peterisza/temu-garden-lights-hack/controller-firmware/USBX/App/ux_device_descriptors.c

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

/* Includes ------------------------------------------------------------------*/
#include "ux_device_descriptors.h"

USBD_DevClassHandleTypeDef  USBD_Device_FS, USBD_Device_HS;

uint8_t UserClassInstance[USBD_MAX_CLASS_INTERFACES] = {
  CLASS_TYPE_HID,
};

uint8_t UserHIDInterface[] = {
  INTERFACE_HID_CUSTOM,
};

/* The generic device descriptor buffer that will be filled by builder
   Size of the buffer is the maximum possible device FS descriptor size. */
#if defined ( __ICCARM__ ) /* IAR Compiler */
#pragma data_alignment=4
#endif /* defined ( __ICCARM__ ) */
__ALIGN_BEGIN static uint8_t DevFrameWorkDesc_FS[USBD_FRAMEWORK_MAX_DESC_SZ] __ALIGN_END = {0};

/* The generic device descriptor buffer that will be filled by builder
   Size of the buffer is the maximum possible device HS descriptor size. */
#if defined ( __ICCARM__ ) /* IAR Compiler */
#pragma data_alignment=4
#endif /* defined ( __ICCARM__ ) */
__ALIGN_BEGIN static uint8_t DevFrameWorkDesc_HS[USBD_FRAMEWORK_MAX_DESC_SZ] __ALIGN_END = {0};

static uint8_t *pDevFrameWorkDesc_FS = DevFrameWorkDesc_FS;

static uint8_t *pDevFrameWorkDesc_HS = DevFrameWorkDesc_HS;
/* String Device Framework :
 Byte 0 and 1 : Word containing the language ID : 0x0904 for US
 Byte 2       : Byte containing the index of the descriptor
 Byte 3       : Byte containing the length of the descriptor string
*/
#if defined ( __ICCARM__ ) /* IAR Compiler */
#pragma data_alignment=4
#endif /* defined ( __ICCARM__ ) */
__ALIGN_BEGIN UCHAR USBD_string_framework[USBD_STRING_FRAMEWORK_MAX_LENGTH]
__ALIGN_END = {0};

/* Multiple languages are supported on the device, to add
   a language besides English, the Unicode language code must
   be appended to the language_id_framework array and the length
   adjusted accordingly. */

#if defined ( __ICCARM__ ) /* IAR Compiler */
#pragma data_alignment=4
#endif /* defined ( __ICCARM__ ) */
__ALIGN_BEGIN UCHAR USBD_language_id_framework[LANGUAGE_ID_MAX_LENGTH]
__ALIGN_END = {0};

#if USBD_HID_CUSTOM_ACTIVATED == 1U

#if defined ( __ICCARM__ ) /* IAR Compiler */
#pragma data_alignment=4
#endif /* defined ( __ICCARM__ ) */
__ALIGN_BEGIN uint8_t USBD_CustomHID_ReportDesc[]
__ALIGN_END =
{
  /* USER CODE BEGIN USBD_CustomHID_ReportDesc */
	  0x06, 0x00, 0xFF,  // Usage Page (Vendor Defined 0xFF00)
	  0x09, 0x01,        // Usage (Vendor Usage 1)
	  0xA1, 0x01,        // Collection (Application)

	  // INPUT REPORT (MCU -> PC): 64 bájt
	  0x09, 0x01,        // Usage
	  0x15, 0x00,        // Logical Minimum (0)
	  0x26, 0xFF, 0x00,  // Logical Maximum (255)
	  0x75, 0x08,        // Report Size (8 bits)
	  0x95, 0x40,        // Report Count (64 bytes = 0x40)
	  0x81, 0x02,        // Input (Data, Variable, Absolute)

	  // OUTPUT REPORT (PC -> MCU): 64 bájt
	  0x09, 0x01,        // Usage
	  0x15, 0x00,        // Logical Minimum (0)
	  0x26, 0xFF, 0x00,  // Logical Maximum (255)
	  0x75, 0x08,        // Report Size (8 bits)
	  0x95, 0x40,        // Report Count (64 bytes = 0x40)
	  0x91, 0x02,        // Output (Data, Variable, Absolute)

  /* USER CODE END USBD_CustomHID_ReportDesc */
  0xc0                          /* End Collection                       */
};

#endif /* USBD_HID_CUSTOM_ACTIVATED == 1U */

static void USBD_Desc_GetString(uint8_t *desc, uint8_t *Buffer, uint16_t *len);
static uint8_t USBD_Desc_GetLen(uint8_t *buf);

static uint8_t *USBD_Device_Framework_Builder(USBD_DevClassHandleTypeDef *pdev,
                                              uint8_t *pDevFrameWorkDesc,
                                              uint8_t *UserClassInstance,
                                              uint8_t Speed);

static uint8_t USBD_FrameWork_AddToConfDesc(USBD_DevClassHandleTypeDef *pdev,
                                            uint8_t Speed,
                                            uint8_t *pCmpstConfDesc);

static uint8_t USBD_FrameWork_AddClass(USBD_DevClassHandleTypeDef *pdev,
                                       USBD_CompositeClassTypeDef class,
                                       uint8_t cfgidx, uint8_t Speed,
                                       uint8_t *pCmpstConfDesc);

static uint8_t USBD_FrameWork_FindFreeIFNbr(USBD_DevClassHandleTypeDef *pdev);

static void USBD_FrameWork_AddConfDesc(uint32_t Conf, uint32_t *pSze);

static void USBD_FrameWork_AssignEp(USBD_DevClassHandleTypeDef *pdev, uint8_t Add,
                                    uint8_t Type, uint32_t Sze);

#if USBD_HID_CLASS_ACTIVATED == 1U
static void USBD_FrameWork_HID_Desc(USBD_DevClassHandleTypeDef *pdev,
                                    uint32_t pConf, uint32_t *Sze);
#endif /* USBD_HID_CLASS_ACTIVATED == 1U */

/**
  * @brief  USBD_Get_Device_Framework_Speed
  *         Return the device speed descriptor
  * @param  Speed : HIGH or FULL SPEED flag
  * @param  length : length of HIGH or FULL SPEED array
  * @retval Pointer to descriptor buffer
  */
uint8_t *USBD_Get_Device_Framework_Speed(uint8_t Speed, ULONG *Length)
{
  uint8_t *pFrameWork = NULL;
  if (USBD_FULL_SPEED == Speed)
  {
    USBD_Device_Framework_Builder(&USBD_Device_FS, pDevFrameWorkDesc_FS,
                                  UserClassInstance, Speed);

    /* Get the length of USBD_device_framework_full_speed */
    *Length = (ULONG)(USBD_Device_FS.CurrDevDescSz + USBD_Device_FS.CurrConfDescSz);

    pFrameWork = pDevFrameWorkDesc_FS;
  }
  else
  {
    USBD_Device_Framework_Builder(&USBD_Device_HS, pDevFrameWorkDesc_HS,
                                  UserClassInstance, Speed);

    /* Get the length of USBD_device_framework_high_speed */
    *Length = (ULONG)(USBD_Device_HS.CurrDevDescSz + USBD_Device_HS.CurrConfDescSz);

    pFrameWork = pDevFrameWorkDesc_HS;
  }
  return pFrameWork;
}

/**
  * @brief  USBD_Get_String_Framework
  *         Return the language_id_framework
  * @param  Length : Length of String_Framework
  * @retval Pointer to language_id_framework buffer
  */
uint8_t *USBD_Get_String_Framework(ULONG *Length)
{
  uint16_t len = 0U;
  uint8_t count = 0U;

  /* Set the Manufacturer language Id and index in USBD_string_framework */
  USBD_string_framework[count++] = USBD_LANGID_STRING & 0xFF;
  USBD_string_framework[count++] = USBD_LANGID_STRING >> 8;
  USBD_string_framework[count++] = USBD_IDX_MFC_STR;

  /* Set the Manufacturer string in string_framework */
  USBD_Desc_GetString((uint8_t *)USBD_MANUFACTURER_STRING, USBD_string_framework + count, &len);

  /* Set the Product language Id and index in USBD_string_framework */
  count += len + 1;
  USBD_string_framework[count++] = USBD_LANGID_STRING & 0xFF;
  USBD_string_framework[count++] = USBD_LANGID_STRING >> 8;
  USBD_string_framework[count++] = USBD_IDX_PRODUCT_STR;

  /* Set the Product string in USBD_string_framework */
  USBD_Desc_GetString((uint8_t *)USBD_PRODUCT_STRING, USBD_string_framework + count, &len);

  /* Set Serial language Id and index in string_framework */
  count += len + 1;
  USBD_string_framework[count++] = USBD_LANGID_STRING & 0xFF;
  USBD_string_framework[count++] = USBD_LANGID_STRING >> 8;
  USBD_string_framework[count++] = USBD_IDX_SERIAL_STR;

  /* Set the Serial number in USBD_string_framework */
  USBD_Desc_GetString((uint8_t *)USBD_SERIAL_NUMBER, USBD_string_framework + count, &len);

  /* Get the length of USBD_string_framework */
  *Length = strlen((const char *)USBD_string_framework);

  return USBD_string_framework;
}

/**
  * @brief  USBD_Get_Language_Id_Framework
  *         Return the language_id_framework
  * @param  Length : Length of Language_Id_Framework
  * @retval Pointer to language_id_framework buffer
  */
uint8_t *USBD_Get_Language_Id_Framework(ULONG *Length)
{
  uint8_t count = 0U;

  /* Set the language Id in USBD_language_id_framework */
  USBD_language_id_framework[count++] = USBD_LANGID_STRING & 0xFF;
  USBD_language_id_framework[count++] = USBD_LANGID_STRING >> 8;

  /* Get the length of USBD_language_id_framework */
  *Length = strlen((const char *)USBD_language_id_framework);

  return USBD_language_id_framework;
}

/**
  * @brief  USBD_Get_Interface_Number
  *         Return interface number
  * @param  class_type : Device class type
  * @param  interface_type : Device interface type
  * @retval interface number
  */
uint16_t USBD_Get_Interface_Number(uint8_t class_type, uint8_t interface_type)
{
  uint8_t itf_num = 0U;
  uint8_t idx = 0U;

  for(idx = 0; idx < USBD_MAX_SUPPORTED_CLASS; idx++)
  {
    if ((USBD_Device_FS.tclasslist[idx].ClassType == class_type) &&
        (USBD_Device_FS.tclasslist[idx].InterfaceType == interface_type))
    {
      itf_num = USBD_Device_FS.tclasslist[idx].Ifs[0];
    }
  }

  return itf_num;
}

/**
  * @brief  USBD_Get_Configuration_Number
  *         Return configuration number
  * @param  class_type : Device class type
  * @param  interface_type : Device interface type
  * @retval configuration number
  */
uint16_t USBD_Get_Configuration_Number(uint8_t class_type, uint8_t interface_type)
{
  uint8_t cfg_num = 1U;

  return cfg_num;
}

#if USBD_HID_CLASS_ACTIVATED == 1U
/**
  * @brief  USBD_HID_ReportDesc
  *         Return the device HID Report Descriptor
  * @param  hid_type : HID Device type
  * @retval Pointer to HID Report Descriptor buffer
  */
uint8_t *USBD_HID_ReportDesc(uint8_t hid_type)
{
  uint8_t *pHidReportDesc = NULL;

  switch(hid_type)
  {
    case INTERFACE_HID_CUSTOM:
      pHidReportDesc = USBD_CustomHID_ReportDesc;
      break;
    default:
      break;
  }

  return pHidReportDesc;
}

/**
  * @brief  USBD_HID_ReportDesc_length
  *         Return the device HID Report Descriptor
  * @param  hid_type : HID Device type
  * @retval Size of HID Report Descriptor buffer
  */
uint16_t USBD_HID_ReportDesc_length(uint8_t hid_type)
{
  uint16_t ReportDesc_Size = 0;

  switch(hid_type)
  {
    case INTERFACE_HID_CUSTOM:
      ReportDesc_Size = sizeof(USBD_CustomHID_ReportDesc);
      break;
    default:
      break;
  }

  return ReportDesc_Size;
}
#endif /* USBD_HID_CLASS_ACTIVATED == 1U */

/**
  * @brief  USBD_Desc_GetString
  *         Convert ASCII string into Unicode one
  * @param  desc : descriptor buffer
  * @param  Unicode : Formatted string buffer (Unicode)
  * @param  len : descriptor length
  * @retval None
  */
static void USBD_Desc_GetString(uint8_t *desc, uint8_t *unicode, uint16_t *len)
{
  uint8_t idx = 0U;
  uint8_t *pdesc;

  if (desc == NULL)
  {
    return;
  }

  pdesc = desc;
  *len = (uint16_t)USBD_Desc_GetLen(pdesc);

  unicode[idx++] = *(uint8_t *)len;

  while (*pdesc != (uint8_t)'\0')
  {
    unicode[idx++] = *pdesc;
    pdesc++;
  }
}

/**
  * @brief  USBD_Desc_GetLen
  *         return the string length
  * @param  buf : pointer to the ASCII string buffer
  * @retval string length
  */
static uint8_t USBD_Desc_GetLen(uint8_t *buf)
{
  uint8_t  len = 0U;
  uint8_t *pbuff = buf;

  while (*pbuff != (uint8_t)'\0')
  {
    len++;
    pbuff++;
  }

  return len;
}

/**
  * @brief  USBD_Device_Framework_Builder
  *         Device Framework builder
  * @param  pdev: device instance
  * @param  pDevFrameWorkDesc: Pointer to the device framework descriptor
  * @param  UserClassInstance: type of the class to be added
  * @param  Speed: Speed parameter HS or FS
  * @retval status
  */
static uint8_t *USBD_Device_Framework_Builder(USBD_DevClassHandleTypeDef *pdev,
                                              uint8_t *pDevFrameWorkDesc,
                                              uint8_t *UserClassInstance,
                                              uint8_t Speed)
{
  static USBD_DeviceDescTypedef   *pDevDesc;
  static USBD_DevQualiDescTypedef *pDevQualDesc;
  uint8_t Idx_Instance = 0U;

  /* Set Dev and conf descriptors size to 0 */
  pdev->CurrConfDescSz = 0U;
  pdev->CurrDevDescSz = 0U;

  /* Set the pointer to the device descriptor area*/
  pDevDesc = (USBD_DeviceDescTypedef *)pDevFrameWorkDesc;

  /* Start building the generic device descriptor common part */
  pDevDesc->bLength = (uint8_t)sizeof(USBD_DeviceDescTypedef);
  pDevDesc->bDescriptorType = UX_DEVICE_DESCRIPTOR_ITEM;
  pDevDesc->bcdUSB = USB_BCDUSB;
  pDevDesc->bDeviceClass = 0x00;
  pDevDesc->bDeviceSubClass = 0x00;
  pDevDesc->bDeviceProtocol = 0x00;
  pDevDesc->bMaxPacketSize = USBD_MAX_EP0_SIZE;
  pDevDesc->idVendor = USBD_VID;
  pDevDesc->idProduct = USBD_PID;
  pDevDesc->bcdDevice = 0x0200;
  pDevDesc->iManufacturer = USBD_IDX_MFC_STR;
  pDevDesc->iProduct = USBD_IDX_PRODUCT_STR;
  pDevDesc->iSerialNumber = USBD_IDX_SERIAL_STR;
  pDevDesc->bNumConfigurations = USBD_MAX_NUM_CONFIGURATION;
  pdev->CurrDevDescSz += (uint32_t)sizeof(USBD_DeviceDescTypedef);

  /* Check if USBx is in high speed mode to add qualifier descriptor */
  if (Speed == USBD_HIGH_SPEED)
  {
    pDevQualDesc = (USBD_DevQualiDescTypedef *)(pDevFrameWorkDesc + pdev->CurrDevDescSz);
    pDevQualDesc->bLength = (uint8_t)sizeof(USBD_DevQualiDescTypedef);
    pDevQualDesc->bDescriptorType = UX_DEVICE_QUALIFIER_DESCRIPTOR_ITEM;
    pDevQualDesc->bcdDevice = 0x0200;
    pDevQualDesc->Class = 0x00;
    pDevQualDesc->SubClass = 0x00;
    pDevQualDesc->Protocol = 0x00;
    pDevQualDesc->bMaxPacketSize = 0x40;
    pDevQualDesc->bNumConfigurations = 0x01;
    pDevQualDesc->bReserved = 0x00;
    pdev->CurrDevDescSz += (uint32_t)sizeof(USBD_DevQualiDescTypedef);
  }

  /* Build the device framework */
  while (Idx_Instance < USBD_MAX_SUPPORTED_CLASS)
  {
    if ((pdev->classId < USBD_MAX_SUPPORTED_CLASS) &&
        (pdev->NumClasses < USBD_MAX_SUPPORTED_CLASS) &&
        (UserClassInstance[Idx_Instance] != CLASS_TYPE_NONE))
    {
      /* Call the composite class builder */
      (void)USBD_FrameWork_AddClass(pdev,
                                    (USBD_CompositeClassTypeDef)UserClassInstance[Idx_Instance],
                                    0, Speed,
                                    (pDevFrameWorkDesc + pdev->CurrDevDescSz));

      /* Increment the ClassId for the next occurrence */
      pdev->classId ++;
      pdev->NumClasses ++;
    }

    Idx_Instance++;
  }

  /* Check if there is a composite class and update device class */
  if (pdev->NumClasses > 1)
  {
    pDevDesc->bDeviceClass = 0xEF;
    pDevDesc->bDeviceSubClass = 0x02;
    pDevDesc->bDeviceProtocol = 0x01;
  }
  else
  {
    /* Check if the CDC ACM class is set and update device class */
    if (UserClassInstance[0] == CLASS_TYPE_CDC_ACM)
    {
      pDevDesc->bDeviceClass = 0x02;
      pDevDesc->bDeviceSubClass = 0x02;
      pDevDesc->bDeviceProtocol = 0x00;
    }
  }

  return pDevFrameWorkDesc;
}

/**
  * @brief  USBD_FrameWork_AddClass
  *         Register a class in the class builder
  * @param  pdev: device instance
  * @param  class: type of the class to be added (from USBD_CompositeClassTypeDef)
  * @param  cfgidx: configuration index
  * @param  speed: device speed
  * @param  pCmpstConfDesc: to composite device configuration descriptor
  * @retval status
  */
uint8_t  USBD_FrameWork_AddClass(USBD_DevClassHandleTypeDef *pdev,
                                 USBD_CompositeClassTypeDef class,
                                 uint8_t cfgidx, uint8_t Speed,
                                 uint8_t *pCmpstConfDesc)
{

  static uint8_t interface_idx = 0U;

  if ((pdev->classId < USBD_MAX_SUPPORTED_CLASS) &&
      (pdev->tclasslist[pdev->classId].Active == 0U))
  {
    /* Store the class parameters in the global tab */
    pdev->tclasslist[pdev->classId].ClassId = pdev->classId;
    pdev->tclasslist[pdev->classId].Active = 1U;
    pdev->tclasslist[pdev->classId].ClassType = class;

    if (class == CLASS_TYPE_HID)
    {
      pdev->tclasslist[pdev->classId].InterfaceType = UserHIDInterface[interface_idx];

      interface_idx++;

      if (interface_idx == sizeof(UserHIDInterface))
      {
        interface_idx = 0U;
      }
    }

    /* Call configuration descriptor builder and endpoint configuration builder */
    if (USBD_FrameWork_AddToConfDesc(pdev, Speed, pCmpstConfDesc) != UX_SUCCESS)
    {
      return UX_ERROR;
    }
  }

  UNUSED(cfgidx);

  return UX_SUCCESS;
}

/**
  * @brief  USBD_FrameWork_AddToConfDesc
  *         Add a new class to the configuration descriptor
  * @param  pdev: device instance
  * @param  Speed: device speed
  * @param  pCmpstConfDesc: to composite device configuration descriptor
  * @retval status
  */
uint8_t  USBD_FrameWork_AddToConfDesc(USBD_DevClassHandleTypeDef *pdev, uint8_t Speed,
                                      uint8_t *pCmpstConfDesc)
{
  uint8_t interface = 0U;

  /* The USB drivers do not set the speed value, so set it here before starting */
  pdev->Speed = Speed;

  /* start building the config descriptor common part */
  if (pdev->classId == 0U)
  {
    /* Add configuration and IAD descriptors */
    USBD_FrameWork_AddConfDesc((uint32_t)pCmpstConfDesc, &pdev->CurrConfDescSz);
  }

  switch (pdev->tclasslist[pdev->classId].ClassType)
  {

#if USBD_HID_CLASS_ACTIVATED == 1U

    case CLASS_TYPE_HID:

      switch(pdev->tclasslist[pdev->classId].InterfaceType)
      {

#if USBD_HID_CUSTOM_ACTIVATED == 1U

        case INTERFACE_HID_CUSTOM:

          /* Find the first available interface slot and Assign number of interfaces */
          interface = USBD_FrameWork_FindFreeIFNbr(pdev);
          pdev->tclasslist[pdev->classId].NumIf = 1U;
          pdev->tclasslist[pdev->classId].Ifs[0] = interface;

          /* Assign endpoint numbers */
          pdev->tclasslist[pdev->classId].NumEps = 2U; /* EP_IN, EP_OUT */

          /* Check the current speed to assign endpoints */
          if (pdev->Speed == USBD_HIGH_SPEED)
          {
            /* Assign IN Endpoint */
            USBD_FrameWork_AssignEp(pdev, USBD_HID_CUSTOM_EPIN_ADDR,
                                    USBD_EP_TYPE_INTR, USBD_HID_CUSTOM_EPIN_HS_MPS);

            /* Assign OUT Endpoint */
            USBD_FrameWork_AssignEp(pdev, USBD_HID_CUSTOM_EPOUT_ADDR,
                                    USBD_EP_TYPE_INTR, USBD_HID_CUSTOM_EPOUT_HS_MPS);
          }
          else
          {
            /* Assign IN Endpoint */
            USBD_FrameWork_AssignEp(pdev, USBD_HID_CUSTOM_EPIN_ADDR,
                                    USBD_EP_TYPE_INTR, USBD_HID_CUSTOM_EPIN_FS_MPS);

            /* Assign OUT Endpoint */
            USBD_FrameWork_AssignEp(pdev, USBD_HID_CUSTOM_EPOUT_ADDR,
                                    USBD_EP_TYPE_INTR, USBD_HID_CUSTOM_EPOUT_FS_MPS);
          }

          /* Configure and Append the Descriptor */
          USBD_FrameWork_HID_Desc(pdev, (uint32_t)pCmpstConfDesc, &pdev->CurrConfDescSz);

          break;

#endif /* USBD_HID_CUSTOM_ACTIVATED == 1U */

        default:
          break;
      }

      break;
#endif /* USBD_HID_CLASS_ACTIVATED == 1U */

    default:
      break;
  }

  return UX_SUCCESS;
}

/**
  * @brief  USBD_FrameWork_FindFreeIFNbr
  *         Find the first interface available slot
  * @param  pdev: device instance
  * @retval The interface number to be used
  */
static uint8_t USBD_FrameWork_FindFreeIFNbr(USBD_DevClassHandleTypeDef *pdev)
{
  uint32_t idx = 0U;

  /* Unroll all already activated classes */
  for (uint32_t i = 0U; i < pdev->NumClasses; i++)
  {
    /* Unroll each class interfaces */
    for (uint32_t j = 0U; j < pdev->tclasslist[i].NumIf; j++)
    {
      /* Increment the interface counter index */
      idx++;
    }
  }

  /* Return the first available interface slot */
  return (uint8_t)idx;
}

/**
  * @brief  USBD_FrameWork_AddConfDesc
  *         Add a new class to the configuration descriptor
  * @param  Conf: configuration descriptor
  * @param  pSze: pointer to the configuration descriptor size
  * @retval none
  */
static void  USBD_FrameWork_AddConfDesc(uint32_t Conf, uint32_t *pSze)
{
  /* Intermediate variable to comply with MISRA-C Rule 11.3 */
  USBD_ConfigDescTypedef *ptr = (USBD_ConfigDescTypedef *)Conf;

  ptr->bLength = (uint8_t)sizeof(USBD_ConfigDescTypedef);
  ptr->bDescriptorType = USB_DESC_TYPE_CONFIGURATION;
  ptr->wDescriptorLength = 0U;
  ptr->bNumInterfaces = 0U;
  ptr->bConfigurationValue = 1U;
  ptr->iConfiguration = USBD_CONFIG_STR_DESC_IDX;
  ptr->bmAttributes = USBD_CONFIG_BMATTRIBUTES;
  ptr->bMaxPower = USBD_CONFIG_MAXPOWER;
  *pSze += sizeof(USBD_ConfigDescTypedef);
}

/**
  * @brief  USBD_FrameWork_AssignEp
  *         Assign and endpoint
  * @param  pdev: device instance
  * @param  Add: Endpoint address
  * @param  Type: Endpoint type
  * @param  Sze: Endpoint max packet size
  * @retval none
  */
static void  USBD_FrameWork_AssignEp(USBD_DevClassHandleTypeDef *pdev,
                                     uint8_t Add, uint8_t Type, uint32_t Sze)
{
  uint32_t idx = 0U;

  /* Find the first available endpoint slot */
  while (((idx < (pdev->tclasslist[pdev->classId]).NumEps) && \
          ((pdev->tclasslist[pdev->classId].Eps[idx].is_used) != 0U)))
  {
    /* Increment the index */
    idx++;
  }

  /* Configure the endpoint */
  pdev->tclasslist[pdev->classId].Eps[idx].add = Add;
  pdev->tclasslist[pdev->classId].Eps[idx].type = Type;
  pdev->tclasslist[pdev->classId].Eps[idx].size = (uint16_t) Sze;
  pdev->tclasslist[pdev->classId].Eps[idx].is_used = 1U;
}

#if USBD_HID_CLASS_ACTIVATED == 1U
/**
  * @brief  USBD_FrameWork_HID_Desc
  *         Configure and Append the HID Descriptor
  * @param  pdev: device instance
  * @param  pConf: Configuration descriptor pointer
  * @param  Sze: pointer to the current configuration descriptor size
  * @retval None
  */
static void  USBD_FrameWork_HID_Desc(USBD_DevClassHandleTypeDef *pdev,
                                     uint32_t pConf, uint32_t *Sze)
{
  static USBD_IfDescTypedef       *pIfDesc;
  static USBD_EpDescTypedef       *pEpDesc;
  static USBD_HIDDescTypedef      *pHidDesc;

  switch(pdev->tclasslist[pdev->classId].InterfaceType)
  {

#if USBD_HID_CUSTOM_ACTIVATED == 1U
    case  INTERFACE_HID_CUSTOM:

      /* Append HID Interface descriptor to Configuration descriptor */
      __USBD_FRAMEWORK_SET_IF(pdev->tclasslist[pdev->classId].Ifs[0], 0U, \
                              (uint8_t)(pdev->tclasslist[pdev->classId].NumEps),
                              UX_DEVICE_CLASS_HID_CLASS,
                              0x00U, INTERFACE_HID_CUSTOM, 0U);

      /* Append HID Functional descriptor to Configuration descriptor */
      pHidDesc = ((USBD_HIDDescTypedef *)(pConf + *Sze));
      pHidDesc->bLength = (uint8_t)sizeof(USBD_HIDDescTypedef);
      pHidDesc->bDescriptorType = UX_DEVICE_CLASS_HID_DESCRIPTOR_HID;
      pHidDesc->bcdHID = 0x0111U;
      pHidDesc->bCountryCode = 0x00U;
      pHidDesc->bNumDescriptors = 0x01U;
      pHidDesc->bHIDDescriptorType = 0x22U;
      pHidDesc->wDescriptorLength = USBD_HID_ReportDesc_length(INTERFACE_HID_CUSTOM);
      *Sze += (uint32_t)sizeof(USBD_HIDDescTypedef);

      if (pdev->Speed == USBD_HIGH_SPEED)
      {
        /* Append Endpoint descriptor to Configuration descriptor */
        __USBD_FRAMEWORK_SET_EP(pdev->tclasslist[pdev->classId].Eps[0].add,
                                USBD_EP_TYPE_INTR,
                                (uint16_t)pdev->tclasslist[pdev->classId].Eps[0].size,
                                USBD_HID_CUSTOM_EPIN_FS_BINTERVAL,
                                USBD_HID_CUSTOM_EPIN_HS_BINTERVAL);

        __USBD_FRAMEWORK_SET_EP(pdev->tclasslist[pdev->classId].Eps[1].add,
                                USBD_EP_TYPE_INTR,
                                (uint16_t)pdev->tclasslist[pdev->classId].Eps[1].size,
                                USBD_HID_CUSTOM_EPOUT_HS_BINTERVAL,
                                USBD_HID_CUSTOM_EPOUT_FS_BINTERVAL);
      }
      else
      {
        /* Append Endpoint descriptor to Configuration descriptor */
        __USBD_FRAMEWORK_SET_EP(pdev->tclasslist[pdev->classId].Eps[0].add,
                                USBD_EP_TYPE_INTR,
                                (uint16_t)pdev->tclasslist[pdev->classId].Eps[0].size,
                                USBD_HID_CUSTOM_EPIN_FS_BINTERVAL,
                                USBD_HID_CUSTOM_EPIN_HS_BINTERVAL);

        __USBD_FRAMEWORK_SET_EP(pdev->tclasslist[pdev->classId].Eps[1].add,
                                USBD_EP_TYPE_INTR,
                                (uint16_t)pdev->tclasslist[pdev->classId].Eps[1].size,
                                USBD_HID_CUSTOM_EPOUT_HS_BINTERVAL,
                                USBD_HID_CUSTOM_EPOUT_FS_BINTERVAL);
      }

      break;

#endif /* USBD_HID_CUSTOM_ACTIVATED == 1U */

    default:
      break;
  }

  /* Update Config Descriptor and IAD descriptor */
  ((USBD_ConfigDescTypedef *)pConf)->bNumInterfaces += 1U;
  ((USBD_ConfigDescTypedef *)pConf)->wDescriptorLength = *Sze;

}
#endif /* USBD_HID_CLASS_ACTIVATED */
