peterisza/temu-garden-lights-hack/controller-firmware/USBX/App/ux_device_customhid.c

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

/* Includes ------------------------------------------------------------------*/
#include "ux_device_customhid.h"

/* USER CODE BEGIN Includes */
#include "main.h"
/* USER CODE END Includes */

/**
  * @brief  USBD_Custom_HID_Activate
  *         This function is called when insertion of a Custom HID device.
  * @param  hid_instance: Pointer to the hid class instance.
  * @retval none
  */
VOID USBD_Custom_HID_Activate(VOID *hid_instance)
{
  /* USER CODE BEGIN USBD_Custom_HID_Activate */
  UX_PARAMETER_NOT_USED(hid_instance);
  /* USER CODE END USBD_Custom_HID_Activate */

  return;
}

/**
  * @brief  USBD_Custom_HID_Deactivate
  *         This function is called when extraction of a Custom HID device.
  * @param  hid_instance: Pointer to the hid class instance.
  * @retval none
  */
VOID USBD_Custom_HID_Deactivate(VOID *hid_instance)
{
  /* USER CODE BEGIN USBD_Custom_HID_Deactivate */
  UX_PARAMETER_NOT_USED(hid_instance);
  /* USER CODE END USBD_Custom_HID_Deactivate */

  return;
}

/**
  * @brief  USBD_Custom_HID_SetFeature
  *         This function is invoked when the host sends a HID SET_REPORT
  *         to the application over Endpoint 0 (Set Feature).
  * @param  hid_instance: Pointer to the hid class instance.
  * @param  hid_event: Pointer to structure of the hid event.
  * @retval status
  */
UINT USBD_Custom_HID_SetFeature(UX_SLAVE_CLASS_HID *hid_instance,
                                UX_SLAVE_CLASS_HID_EVENT *hid_event)
{
  UINT status = UX_SUCCESS;

  /* USER CODE BEGIN USBD_Custom_HID_SetFeature */
  UX_PARAMETER_NOT_USED(hid_instance);
  UX_PARAMETER_NOT_USED(hid_event);
  /* USER CODE END USBD_Custom_HID_SetFeature */

  return status;
}

/**
  * @brief  USBD_Custom_HID_GetReport
  *         This function is invoked when host is requesting event through
  *         control GET_REPORT request.
  * @param  hid_instance: Pointer to the hid class instance.
  * @param  hid_event: Pointer to structure of the hid event.
  * @retval status
  */
UINT USBD_Custom_HID_GetReport(UX_SLAVE_CLASS_HID *hid_instance,
                               UX_SLAVE_CLASS_HID_EVENT *hid_event)
{
  UINT status = UX_SUCCESS;

  /* USER CODE BEGIN USBD_Custom_HID_GetReport */
  UX_PARAMETER_NOT_USED(hid_instance);
  UX_PARAMETER_NOT_USED(hid_event);
  /* USER CODE END USBD_Custom_HID_GetReport */

  return status;
}

#ifdef UX_DEVICE_CLASS_HID_INTERRUPT_OUT_SUPPORT

/**
  * @brief  USBD_Custom_HID_SetReport
  *         This function is invoked when the host sends a HID SET_REPORT
  *         to the application over Endpoint OUT (Set Report).
  * @param  hid_instance: Pointer to the hid class instance.
  * @retval none
  */
VOID USBD_Custom_HID_SetReport(struct UX_SLAVE_CLASS_HID_STRUCT *hid_instance)
{
  /* USER CODE BEGIN USBD_Custom_HID_SetReport */
  //UX_PARAMETER_NOT_USED(hid_instance);

	UX_DEVICE_CLASS_HID_RECEIVED_EVENT hid_event;
	while(ux_device_class_hid_receiver_event_get(hid_instance, &hid_event) == UX_SUCCESS)
	{
	  VerifiedUart_SubmitFrame(&g_uart2,
	      (const uint8_t *)hid_event.ux_device_class_hid_received_event_data,
	      (uint16_t)hid_event.ux_device_class_hid_received_event_length);

	  ux_device_class_hid_receiver_event_free(hid_instance);
	}
/* Itt az adatot a hid_event.ux_device_class_hid_received_event_data tömbben találod,
	 a hosszát pedig a hid_event.ux_device_class_hid_received_event_length változóban. */

  /* USER CODE END USBD_Custom_HID_SetReport */

  return;
}

/**
  * @brief  USBD_Custom_HID_EventMaxNumber
  *         This function to set receiver event max number parameter.
  * @param  none
  * @retval receiver event max number
  */
ULONG USBD_Custom_HID_EventMaxNumber(VOID)
{
  ULONG max_number = 0U;

  /* USER CODE BEGIN USBD_Custom_HID_EventMaxNumber */
  return 4;
  /* USER CODE END USBD_Custom_HID_EventMaxNumber */

  return max_number;
}

/**
  * @brief  USBD_Custom_HID_EventMaxLength
  *         This function to set receiver event max length parameter.
  * @param  none
  * @retval receiver event max length
  */
ULONG USBD_Custom_HID_EventMaxLength(VOID)
{
  ULONG max_length = 0U;

  /* USER CODE BEGIN USBD_Custom_HID_EventMaxLength */
  return 64;
  /* USER CODE END USBD_Custom_HID_EventMaxLength */

  return max_length;
}

#endif /* UX_DEVICE_CLASS_HID_INTERRUPT_OUT_SUPPORT */
